PaulKlinger/mrna_vaccine_badge/pcb/mrna_badge.sch

## EAGLE design pcb/mrna_badge.sch (2021-08-16)

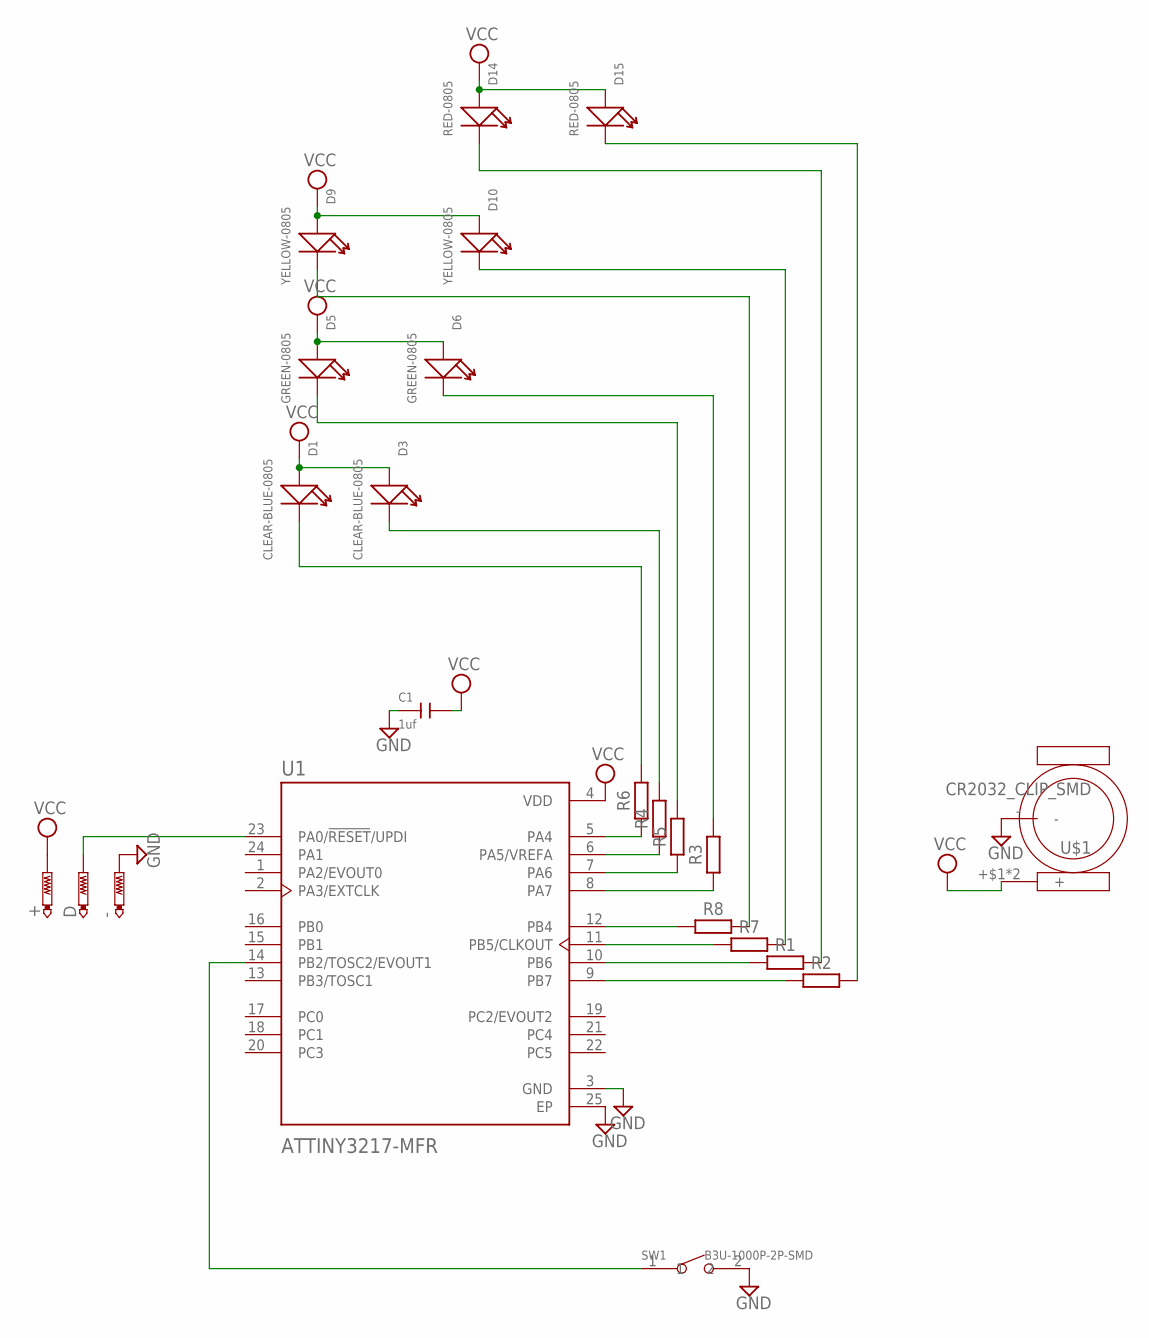
[picture p2: schematic mrna_badge.sch]

Parts:
+: PTR1TP15R; TP15R
-: PTR1TP15R; TP15R
C1: 1uf; C0805
D: PTR1TP15R; TP15R
D1, D3: CLEAR-BLUE-0805; LED-0805
D5, D6: GREEN-0805; LED-0805
D9, D10: YELLOW-0805; LED-0805
D14, D15: RED-0805; LED-0805
R1, R2, R3, R4, R5, R6, R7, R8: R_CHIP-0805(2012-METRIC); RESC2012X65
SW1: B3U-1000P-2P-SMD; SW2-2.6-3.0X2.5X1.2+0.4MM
U1: ATTINY3217-MFR; QFN50P400X400X90-25N
U$1: CR2032_CLIP_SMD; CR2032_SMT_BAT-HLD-001

Connections:
GND: -.TP, C1.1, SW1.2, U1.3 (GND), U1.25 (EP), U$1.-
unnamed: R4.1, U1.6 (PA5/VREFA)
unnamed: R5.1, U1.7 (PA6)
unnamed: D5.-, R5.2
unnamed: R1.1, U1.10 (PB6)
unnamed: R6.1, U1.5 (PA4)
unnamed: R2.1, U1.9 (PB7)
unnamed: R3.1, U1.8 (PA7)
unnamed: D1.-, R6.2
unnamed: SW1.1, U1.14 (PB2/TOSC2/EVOUT1)
unnamed: D.TP, U1.23 (PA0/!RESET!/UPDI)
unnamed: R7.1, U1.11 (PB5/CLKOUT)
unnamed: D3.-, R4.2
unnamed: D6.-, R3.2
unnamed: D10.-, R7.2
unnamed: D15.-, R2.2
unnamed: R8.1, U1.12 (PB4)
unnamed: D9.-, R8.2
unnamed: D14.-, R1.2
VCC: +.TP, C1.2, D1.+, D3.+, D5.+, D6.+, D9.+, D10.+, D14.+, D15.+, U1.4 (VDD), U$1.+$1 (+)
