PaulKlinger/mrna_vaccine_badge/mrna_vaccine_badge_code.X/moderna_sequence.c

#include "sequence.h"


/* Generated from .fasta using encode_genome.py */
/* 2 bits per base, 00:A, 01:C, 10:G, 11:T */
static const uint8_t sequence_data[] = {
168, 12, 34, 32, 8, 34, 194, 8, 12, 194, 21, 105, 150, 81, 78, 246,
239, 94, 185, 231, 149, 122, 226, 73, 75, 155, 129, 120, 81, 90, 21, 39,
148, 82, 92, 69, 4, 159, 69, 106, 155, 113, 197, 88, 66, 187, 214, 137,
38, 215, 145, 36, 84, 161, 123, 215, 149, 247, 210, 65, 184, 94, 189, 70,
83, 81, 184, 154, 69, 6, 145, 66, 107, 216, 65, 86, 231, 149, 244, 24,
105, 187, 31, 101, 36, 88, 130, 36, 19, 77, 106, 158, 141, 246, 145, 69,
122, 18, 66, 21, 34, 94, 120, 219, 131, 6, 81, 65, 186, 227, 66, 187,
152, 189, 75, 222, 65, 133, 95, 94, 166, 236, 113, 68, 32, 65, 8, 158,
142, 136, 152, 189, 106, 236, 73, 38, 80, 65, 228, 95, 98, 198, 226, 82,
87, 215, 142, 133, 232, 169, 9, 42, 65, 244, 32, 94, 106, 47, 110, 244,
32, 77, 134, 156, 125, 8, 220, 73, 9, 17, 84, 52, 23, 174, 106, 55,
149, 74, 159, 116, 149, 232, 149, 122, 232, 94, 84, 218, 77, 4, 209, 90,
245, 33, 94, 122, 87, 145, 104, 156, 94, 21, 74, 97, 36, 146, 106, 232,
73, 41, 154, 121, 241, 198, 234, 113, 121, 37, 90, 23, 215, 158, 11, 16,
98, 6, 145, 77, 22, 25, 110, 135, 153, 94, 133, 119, 137, 136, 80, 185,
21, 224, 137, 244, 91, 162, 10, 147, 113, 72, 82, 65, 245, 171, 146, 84,
88, 137, 54, 230, 189, 84, 19, 69, 5, 238, 85, 246, 152, 174, 244, 25,
69, 107, 217, 73, 187, 25, 122, 5, 160, 154, 52, 144, 121, 186, 88, 113,
38, 231, 177, 4, 153, 73, 244, 145, 125, 11, 156, 105, 184, 149, 69, 9,
224, 97, 123, 159, 69, 6, 236, 101, 132, 159, 110, 53, 186, 97, 138, 230,
146, 54, 69, 105, 72, 74, 66, 54, 88, 113, 7, 16, 158, 86, 24, 125,
22, 158, 110, 54, 94, 129, 36, 16, 93, 132, 144, 174, 166, 144, 113, 7,
23, 177, 105, 239, 90, 8, 144, 94, 9, 95, 98, 106, 19, 73, 22, 35,
113, 66, 90, 117, 21, 126, 65, 166, 232, 169, 244, 30, 113, 245, 119, 146,
39, 26, 125, 73, 81, 65, 166, 234, 113, 73, 92, 90, 186, 235, 158, 39,
216, 158, 121, 25, 84, 148, 91, 187, 165, 80, 130, 36, 80, 94, 184, 32,
66, 230, 224, 125, 7, 208, 105, 124, 90, 69, 166, 231, 133, 136, 144, 66,
3, 215, 149, 253, 36, 189, 165, 168, 77, 150, 17, 69, 134, 123, 154, 141,
84, 133, 122, 35, 94, 132, 209, 87, 228, 159, 105, 166, 226, 110, 52, 85,
41, 20, 17, 73, 5, 43, 165, 185, 236, 82, 134, 224, 121, 22, 43, 149,
186, 83, 81, 150, 20, 158, 17, 81, 122, 106, 220, 73, 22, 146, 65, 187,
212, 133, 106, 90, 249, 120, 218, 101, 137, 27, 129, 4, 156, 98, 230, 19,
85, 54, 153, 105, 55, 185, 73, 197, 33, 82, 20, 61, 21, 104, 169, 10,
38, 233, 73, 72, 147, 77, 151, 17, 78, 37, 234, 101, 136, 18, 110, 151,
18, 65, 4, 147, 101, 53, 81, 65, 244, 83, 73, 184, 81, 98, 61, 229,
110, 36, 225, 66, 20, 155, 161, 228, 83, 177, 55, 154, 97, 36, 88, 185,
36, 23, 158, 121, 44, 105, 39, 222, 69, 73, 224, 90, 149, 225, 105, 54,
91, 162, 74, 16, 129, 21, 40, 174, 246, 84, 174, 9, 35, 113, 8, 85,
213, 52, 40, 125, 166, 159, 65, 244, 148, 141, 121, 88, 85, 36, 37, 73,
9, 162, 125, 54, 40, 94, 123, 208, 66, 184, 87, 37, 134, 90, 125, 52,
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
};

const struct sequence moderna_sequence = {
    .data = (uint8_t*) sequence_data,
    .n_bases = 4080
};
