PaulKlinger/mrna_vaccine_badge/mrna_vaccine_badge_code.X/pfizer_sequence.c

#include "sequence.h"

/* Generated from .fasta using encode_genome.py */
/* 2 bits per base, 00:A, 01:C, 10:G, 11:T */
static const uint8_t sequence_data[] = {
136, 48, 28, 179, 223, 122, 213, 68, 135, 72, 136, 21, 148, 83, 189, 187,
215, 174, 121, 229, 222, 187, 82, 82, 238, 224, 94, 20, 82, 4, 73, 229,
212, 151, 17, 65, 39, 241, 72, 166, 236, 113, 86, 16, 174, 244, 141, 73,
185, 228, 119, 21, 40, 94, 245, 229, 253, 244, 144, 110, 23, 175, 81, 148,
212, 110, 214, 145, 67, 164, 80, 136, 246, 16, 85, 185, 229, 125, 6, 26,
174, 199, 249, 73, 22, 32, 181, 4, 211, 72, 167, 163, 125, 164, 81, 30,
132, 144, 133, 72, 151, 158, 54, 224, 65, 148, 80, 110, 180, 208, 46, 230,
47, 82, 247, 144, 97, 87, 215, 169, 183, 28, 81, 8, 16, 66, 39, 163,
160, 38, 47, 90, 187, 18, 73, 148, 16, 121, 23, 216, 177, 187, 84, 151,
245, 227, 161, 122, 10, 66, 74, 144, 125, 8, 23, 153, 139, 219, 191, 8,
19, 97, 167, 31, 66, 55, 18, 66, 68, 85, 205, 5, 219, 154, 141, 229,
210, 167, 221, 231, 122, 5, 94, 186, 55, 149, 54, 147, 65, 52, 86, 191,
72, 71, 158, 149, 228, 72, 39, 23, 132, 94, 152, 201, 36, 154, 58, 18,
122, 229, 150, 124, 115, 186, 156, 94, 73, 114, 5, 245, 231, 130, 196, 24,
129, 164, 83, 69, 134, 91, 163, 238, 119, 163, 93, 226, 98, 16, 46, 69,
120, 45, 125, 22, 232, 2, 164, 220, 82, 20, 144, 125, 106, 228, 149, 22,
13, 77, 185, 175, 85, 12, 209, 67, 123, 149, 125, 166, 43, 189, 14, 81,
72, 246, 93, 238, 198, 94, 129, 104, 38, 141, 36, 62, 110, 150, 28, 117,
185, 236, 65, 214, 82, 125, 36, 95, 66, 231, 26, 110, 213, 113, 66, 120,
24, 94, 231, 209, 1, 187, 25, 97, 39, 219, 141, 106, 136, 224, 185, 164,
143, 149, 122, 18, 18, 144, 141, 150, 28, 65, 196, 39, 149, 134, 31, 69,
167, 187, 143, 151, 160, 73, 4, 23, 161, 212, 11, 105, 164, 28, 67, 197,
236, 90, 123, 214, 130, 212, 55, 130, 87, 216, 154, 132, 221, 69, 136, 220,
210, 150, 146, 69, 95, 176, 105, 186, 10, 125, 7, 156, 125, 81, 228, 181,
198, 159, 210, 84, 64, 233, 186, 156, 210, 87, 18, 46, 186, 231, 137, 246,
7, 158, 78, 85, 229, 18, 238, 105, 92, 32, 9, 20, 55, 110, 8, 16,
57, 184, 31, 65, 244, 26, 94, 22, 145, 105, 185, 225, 34, 36, 16, 130,
245, 229, 61, 73, 47, 233, 106, 51, 101, 140, 81, 33, 150, 242, 35, 85,
33, 30, 128, 215, 161, 52, 85, 249, 39, 218, 104, 187, 123, 141, 21, 122,
69, 4, 82, 67, 74, 233, 46, 123, 20, 161, 184, 30, 197, 130, 229, 110,
148, 244, 101, 141, 39, 132, 92, 78, 154, 187, 29, 69, 164, 144, 238, 253,
33, 72, 150, 158, 222, 54, 137, 98, 70, 224, 67, 39, 24, 185, 132, 213,
77, 166, 122, 13, 230, 82, 113, 72, 68, 132, 4, 149, 218, 34, 82, 9,
186, 82, 82, 36, 211, 229, 196, 67, 183, 122, 153, 98, 4, 155, 165, 199,
80, 65, 220, 217, 205, 84, 80, 125, 20, 210, 110, 20, 72, 141, 121, 123,
181, 56, 80, 133, 38, 232, 121, 20, 236, 77, 230, 152, 245, 22, 46, 117,
5, 231, 158, 75, 26, 73, 247, 145, 82, 120, 50, 37, 120, 74, 141, 150,
232, 18, 132, 32, 69, 66, 43, 189, 149, 11, 130, 72, 220, 66, 21, 117,
205, 10, 31, 105, 167, 208, 253, 37, 35, 222, 86, 53, 201, 9, 82, 66,
104, 159, 77, 138, 23, 158, 244, 16, 46, 17, 233, 97, 150, 159, 77, 9,
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
};

const struct sequence pfizer_sequence = {
    .data = (uint8_t*) sequence_data,
    .n_bases = 4284
};
