PaulKlinger/mrna_vaccine_badge/mrna_vaccine_badge_code.X/pfizer_sequence.h

/* 
 * File:   pfizer_sequence.h
 * Author: kling
 *
 * Created on 18 July 2021, 21:41
 */

#ifndef PFIZER_SEQUENCE_H
#define	PFIZER_SEQUENCE_H

#ifdef	__cplusplus
extern "C" {
#endif


    #include "sequence.h"
    const struct sequence pfizer_sequence;


#ifdef	__cplusplus
}
#endif

#endif	/* PFIZER_SEQUENCE_H */
