PaulKlinger/mrna_vaccine_badge/mrna_vaccine_badge_code.X/moderna_sequence.h

/* 
 * File:   moderna_sequence.h
 * Author: kling
 *
 * Created on 03 July 2021, 20:42
 */

#ifndef MODERNA_SEQUENCE_H
#define	MODERNA_SEQUENCE_H

#ifdef	__cplusplus
extern "C" {
#endif
    #include "sequence.h"
    const struct sequence moderna_sequence;


#ifdef	__cplusplus
}
#endif

#endif	/* MODERNA_SEQUENCE_H */
